6502-retro/6502-retro-v4/hardware/6502-retro-v4.kicad_sch

## KiCad design hardware/6502-retro-v4.kicad_sch (2026-03-13)

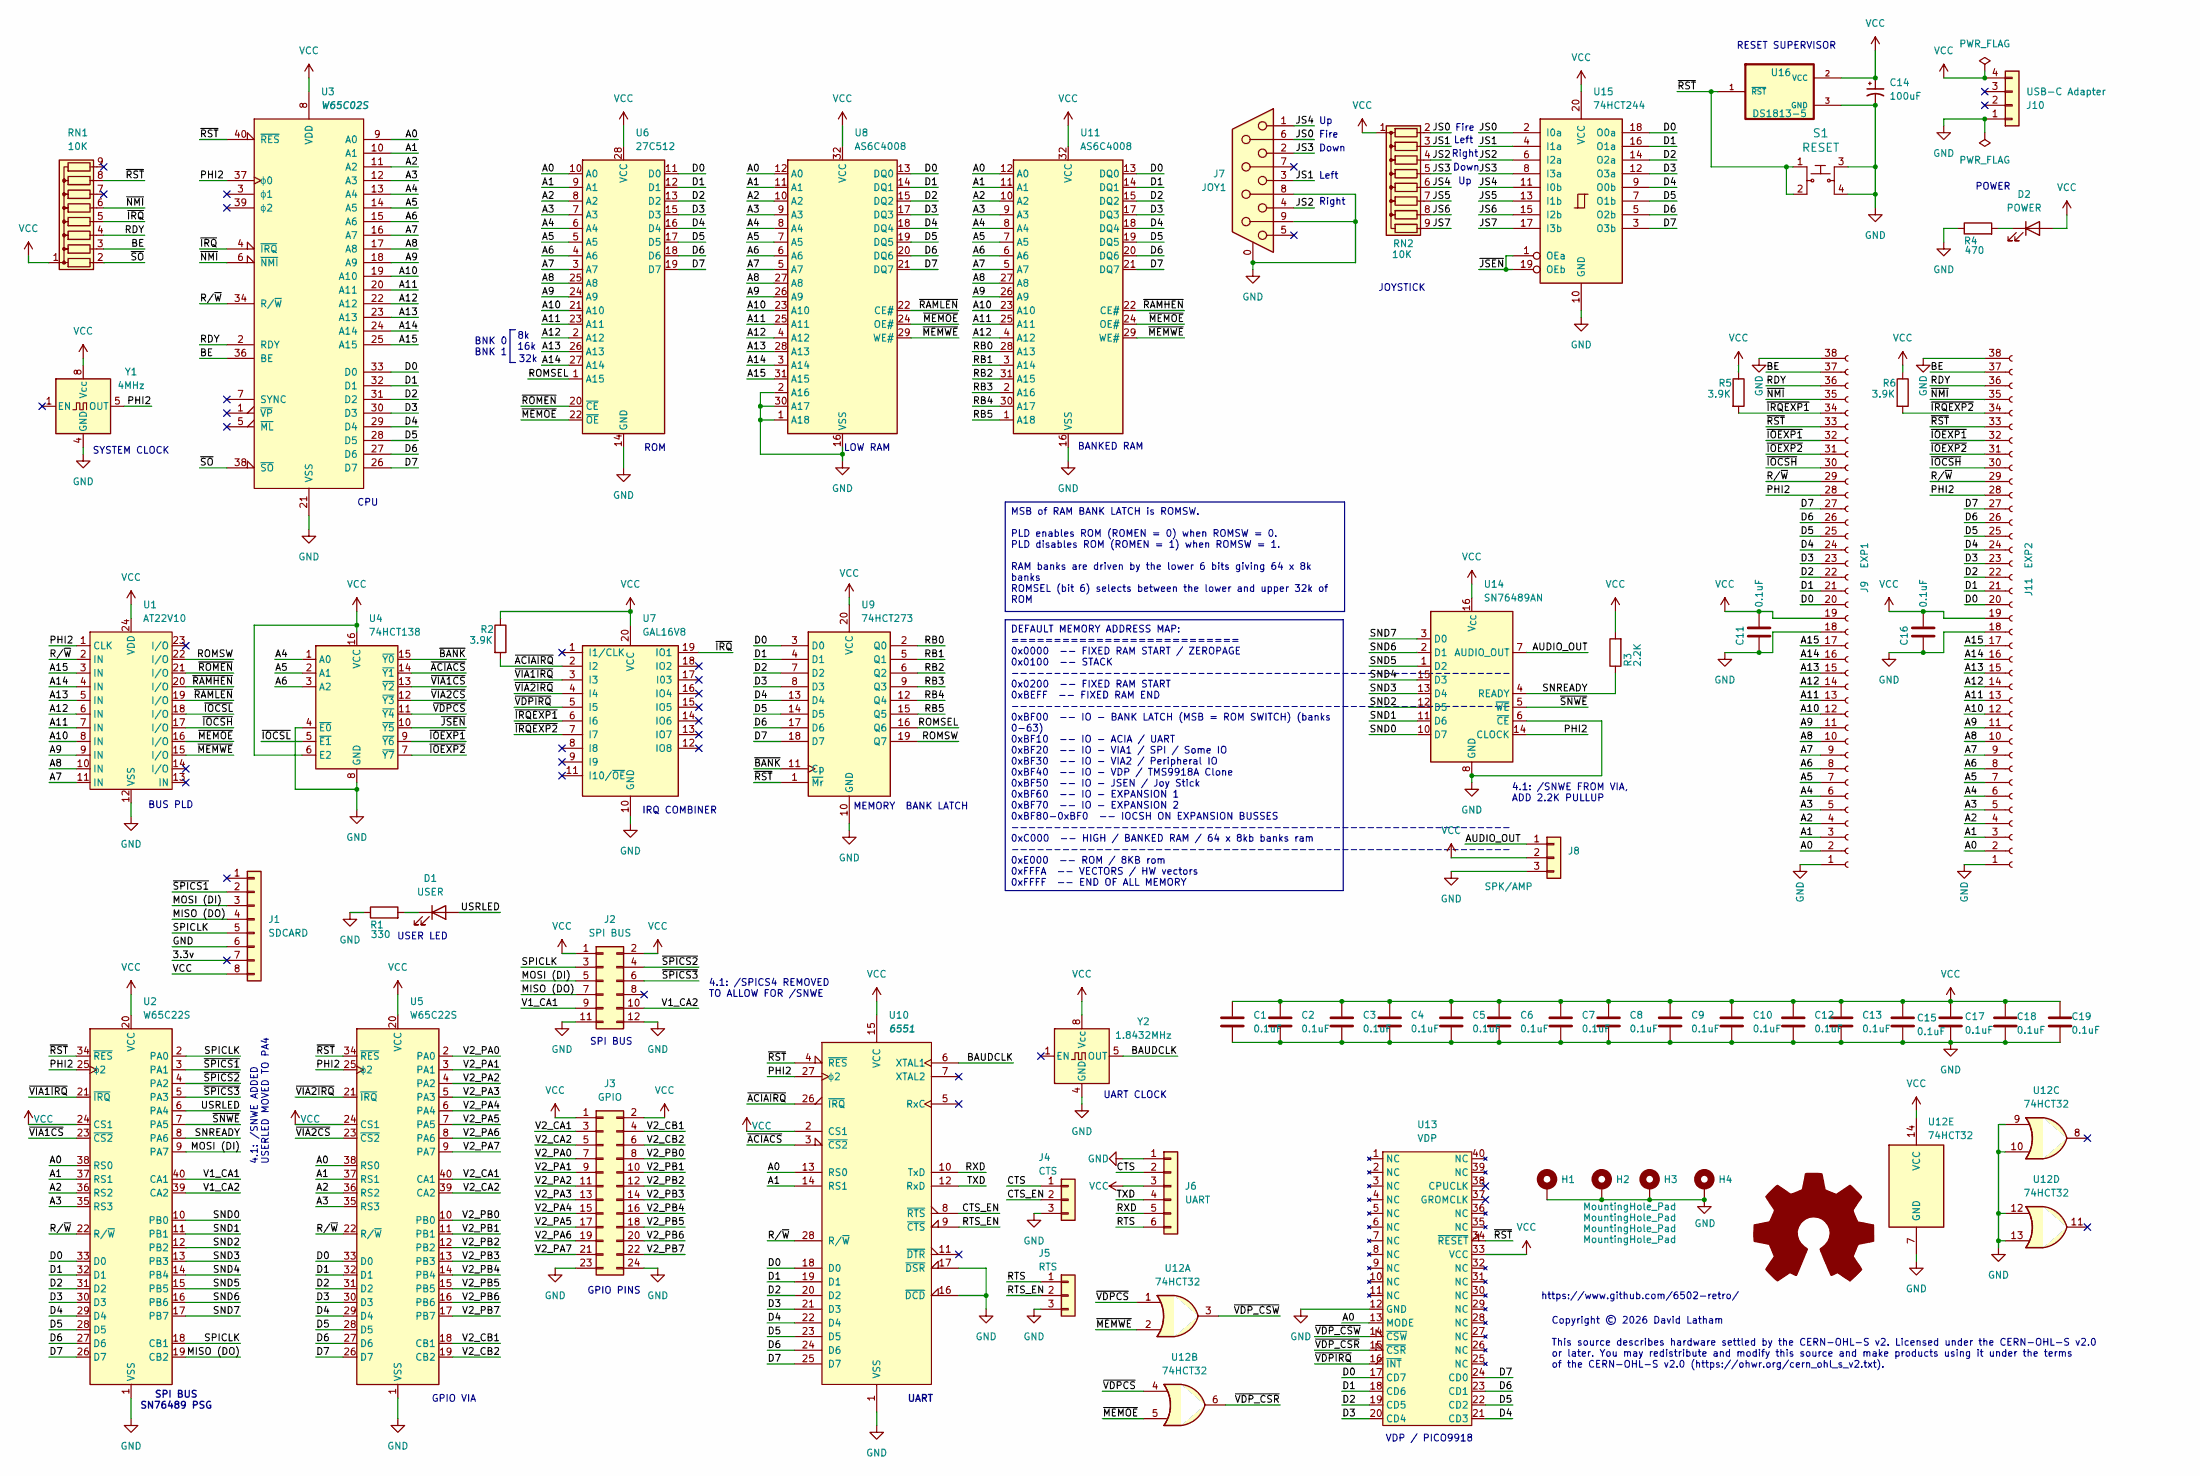
[picture p3: schematic 6502-retro-v4.kicad_sch]

Parts:
C1, C2, C3, C5: 0.1uF; C_Disc_D3.8mm_W2.6mm_P2.50mm
C4, C6, C7, C8, C9, C10, C11, C12, C13, C15, C16, C17, C18, C19: 0.1uF; C_Disc_D3.0mm_W2.0mm_P2.50mm
C14: 100uF; CP_Radial_D5.0mm_P2.50mm
D1: USER; LED_D5.0mm
D2: POWER; LED_D5.0mm
H1, H2, H3, H4: MountingHole_Pad; MountingHole_3.2mm_M3_Pad
J1: SDCARD; PinSocket_1x08_P2.54mm_Vertical
J2: SPI BUS; PinSocket_2x06_P2.54mm_Vertical
J3: GPIO; PinSocket_2x12_P2.54mm_Vertical
J4: CTS; PinHeader_1x03_P2.54mm_Vertical
J5: RTS; PinHeader_1x03_P2.54mm_Vertical
J6: UART; PinSocket_1x06_P2.54mm_Horizontal
J7: JOY1; DSUB-9_Pins_Horizontal_P2.77x2.84mm_EdgePinOffset7.70mm_Hou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
J8: SPK/AMP; PinSocket_1x03_P2.54mm_Vertical
J9: EXP1; PinSocket_1x38_P2.54mm_Vertical
J10: USB-C Adapter; PinSocket_1x04_P2.54mm_Vertical
J11: EXP2; PinSocket_1x38_P2.54mm_Vertical
R1: 330; R_Axial_DIN0204_L3.6mm_D1.6mm_P5.08mm_Horizontal
R2, R5, R6: 3.9K; R_Axial_DIN0204_L3.6mm_D1.6mm_P5.08mm_Horizontal
R3: 2.2K; R_Axial_DIN0204_L3.6mm_D1.6mm_P5.08mm_Horizontal
R4: 470; R_Axial_DIN0204_L3.6mm_D1.6mm_P5.08mm_Horizontal
RN1, RN2: 10K; R_Array_SIP9
S1: RESET; Switch_Tactile_THT_6x6mm; MPN 1825910-6; Digi-Key_PN 450-1650-ND
U1: AT22V10; DIP-24_W7.62mm_Socket
U2, U5: W65C22S; DIP-40_W15.24mm_Socket
U3: W65C02S; DIP-40_W15.24mm_Socket
U4: 74HCT138; DIP-16_W7.62mm_Socket
U6: 27C512; DIP-28_W15.24mm_Socket
U7: GAL16V8; DIP-20_W7.62mm_Socket
U8, U11: AS6C4008; DIP-32_W15.24mm_Socket
U9: 74HCT273; DIP-20_W7.62mm_Socket
U10: 6551; DIP-28_W15.24mm_Socket
U12: 74HCT32; DIP-14_W7.62mm_Socket
U13: VDP; DIP-40_W15.24mm_Socket
U14: SN76489AN; DIP-16_W7.62mm_Socket
U15: 74HCT244; DIP-20_W7.62mm_Socket
U16: DS1813-5; TO-92L_HandSolder
Y1: 4MHz; Oscillator_DIP-8
Y2: 1.8432MHz; Oscillator_DIP-8

Connections:
3.3v: J1.7
A0: J9.2, J11.2, U2.38 (RS0), U3.9 (A0), U5.38 (RS0), U6.10 (A0), U8.12 (A0), U10.13 (RS0), U11.12 (A0), U13.13 (MODE)
A1: J9.3, J11.3, U2.37 (RS1), U3.10 (A1), U5.37 (RS1), U6.9 (A1), U8.11 (A1), U10.14 (RS1), U11.11 (A1)
A2: J9.4, J11.4, U2.36 (RS2), U3.11 (A2), U5.36 (RS2), U6.8 (A2), U8.10 (A2), U11.10 (A2)
A3: J9.5, J11.5, U2.35 (RS3), U3.12 (A3), U5.35 (RS3), U6.7 (A3), U8.9 (A3), U11.9 (A3)
A4: J9.6, J11.6, U3.13 (A4), U4.1 (A0), U6.6 (A4), U8.8 (A4), U11.8 (A4)
A5: J9.7, J11.7, U3.14 (A5), U4.2 (A1), U6.5 (A5), U8.7 (A5), U11.7 (A5)
A6: J9.8, J11.8, U3.15 (A6), U4.3 (A2), U6.4 (A6), U8.6 (A6), U11.6 (A6)
A7: J9.9, J11.9, U1.11 (IN), U3.16 (A7), U6.3 (A7), U8.5 (A7), U11.5 (A7)
A8: J9.10, J11.10, U1.10 (IN), U3.17 (A8), U6.25 (A8), U8.27 (A8), U11.27 (A8)
A9: J9.11, J11.11, U1.9 (IN), U3.18 (A9), U6.24 (A9), U8.26 (A9), U11.26 (A9)
A10: J9.12, J11.12, U1.8 (IN), U3.19 (A10), U6.21 (A10), U8.23 (A10), U11.23 (A10)
A11: J9.13, J11.13, U1.7 (IN), U3.20 (A11), U6.23 (A11), U8.25 (A11), U11.25 (A11)
A12: J9.14, J11.14, U1.6 (IN), U3.22 (A12), U6.2 (A12), U8.4 (A12), U11.4 (A12)
A13: J9.15, J11.15, U1.5 (IN), U3.23 (A13), U6.26 (A13), U8.28 (A13)
A14: J9.16, J11.16, U1.4 (IN), U3.24 (A14), U6.27 (A14), U8.3 (A14)
A15: J9.17, J11.17, U1.3 (IN), U3.25 (A15), U8.31 (A15)
AUDIO_OUT: J8.1, U14.7 (AUDIO_OUT)
BAUDCLK: U10.6 (XTAL1), Y2.5 (OUT)
BE: J9.37, J11.37, RN1.3 (R2), U3.36 (BE)
CTS: J4.1, J6.2
CTS_EN: J4.2, U10.8 (~RTS)
D0: J9.20, J11.20, U2.33 (D0), U3.33 (D0), U5.33 (D0), U6.11 (D0), U8.13 (DQ0), U9.3 (D0), U10.18 (D0), U11.13 (DQ0), U13.17 (CD7), U15.18 (O0a)
D1: J9.21, J11.21, U2.32 (D1), U3.32 (D1), U5.32 (D1), U6.12 (D1), U8.14 (DQ1), U9.4 (D1), U10.19 (D1), U11.14 (DQ1), U13.18 (CD6), U15.16 (O1a)
D2: J9.22, J11.22, U2.31 (D2), U3.31 (D2), U5.31 (D2), U6.13 (D2), U8.15 (DQ2), U9.7 (D2), U10.20 (D2), U11.15 (DQ2), U13.19 (CD5), U15.14 (O2a)
D3: J9.23, J11.23, U2.30 (D3), U3.30 (D3), U5.30 (D3), U6.15 (D3), U8.17 (DQ3), U9.8 (D3), U10.21 (D3), U11.17 (DQ3), U13.20 (CD4), U15.12 (O3a)
D4: J9.24, J11.24, U2.29 (D4), U3.29 (D4), U5.29 (D4), U6.16 (D4), U8.18 (DQ4), U9.13 (D4), U10.22 (D4), U11.18 (DQ4), U13.21 (CD3), U15.9 (O0b)
D5: J9.25, J11.25, U2.28 (D5), U3.28 (D5), U5.28 (D5), U6.17 (D5), U8.19 (DQ5), U9.14 (D5), U10.23 (D5), U11.19 (DQ5), U13.22 (CD2), U15.7 (O1b)
D6: J9.26, J11.26, U2.27 (D6), U3.27 (D6), U5.27 (D6), U6.18 (D6), U8.20 (DQ6), U9.17 (D6), U10.24 (D6), U11.20 (DQ6), U13.23 (CD1), U15.5 (O2b)
D7: J9.27, J11.27, U2.26 (D7), U3.26 (D7), U5.26 (D7), U6.19 (D7), U8.21 (DQ7), U9.18 (D7), U10.25 (D7), U11.21 (DQ7), U13.24 (CD0), U15.3 (O3b)
GND: C1.2, C2.2, C3.2, C4.2, C5.2, C6.2, C7.2, C8.2, C9.2, C10.2, C11.1, C12.2, C13.2, C14.2, C15.2, C16.1, C17.2, C18.2, C19.2, H1.1, H2.1, H3.1, H4.1, J1.6, J2.11, J2.12, J3.23, J3.24, J4.3, J5.3, J6.1, J7.0 (PAD), J7.8, J7.9, J8.3, J9.1, J9.18, J9.38, J10.1, J11.1, J11.18, J11.38, R1.1, R4.1, S1.3, S1.4, U1.12 (VSS), U2.1 (VSS), U3.21 (VSS), U4.4 (~E0), U4.8 (GND), U5.1 (VSS), U6.14 (GND), U7.10 (GND), U8.1 (A18), U8.2 (A16), U8.16 (VSS), U8.30 (A17), U9.10 (GND), U10.1 (VSS), U10.16 (~DCD), U10.17 (~DSR), U11.16 (VSS), U12.7 (GND), U12.9, U12.10, U12.12, U12.13, U13.12 (GND), U14.6 (~CE), U14.8 (GND), U15.10 (GND), U16.3 (GND), Y1.4 (GND), Y2.4 (GND)
JS0: J7.6, RN2.2 (R1), U15.2 (I0a)
JS1: J7.3, RN2.3 (R2), U15.4 (I1a)
JS2: J7.4, RN2.4 (R3), U15.6 (I2a)
JS3: J7.2, RN2.5 (R4), U15.8 (I3a)
JS4: J7.1, RN2.6 (R5), U15.11 (I0b)
JS5: RN2.7 (R6), U15.13 (I1b)
JS6: RN2.8 (R7), U15.15 (I2b)
JS7: RN2.9 (R8), U15.17 (I3b)
MISO (DO): J1.4, J2.7, U2.19 (CB2)
MOSI (DI): J1.3, J2.5, U2.9 (PA7)
unnamed: D1.1 (K), R1.2
unnamed: D2.1 (K), R4.2
PHI2: J9.28, J11.28, U1.1 (CLK), U2.25 (ϕ2), U3.37 (ϕ0), U5.25 (ϕ2), U10.27 (ϕ2), U14.14 (CLOCK), Y1.5 (OUT)
RB0: U9.2 (Q0), U11.28 (A13)
RB1: U9.5 (Q1), U11.3 (A14)
RB2: U9.6 (Q2), U11.31 (A15)
RB3: U9.9 (Q3), U11.2 (A16)
RB4: U9.12 (Q4), U11.30 (A17)
RB5: U9.15 (Q5), U11.1 (A18)
RDY: J9.36, J11.36, RN1.4 (R3), U3.2 (RDY)
ROMSEL: U6.1 (A15), U9.16 (Q6)
ROMSW: U1.22 (I/O), U9.19 (Q7)
RTS: J5.1, J6.6
RTS_EN: J5.2, U10.9 (~CTS)
RXD: J6.5, U10.10 (TxD)
R/~W: J9.29, J11.29, U1.2 (IN), U2.22 (R/~W), U3.34 (R/~W), U5.22 (R/~W), U10.28 (R/~W)
SND0: U2.10 (PB0), U14.10 (D7)
SND1: U2.11 (PB1), U14.11 (D6)
SND2: U2.12 (PB2), U14.12 (D5)
SND3: U2.13 (PB3), U14.13 (D4)
SND4: U2.14 (PB4), U14.15 (D3)
SND5: U2.15 (PB5), U14.1 (D2)
SND6: U2.16 (PB6), U14.2 (D1)
SND7: U2.17 (PB7), U14.3 (D0)
SNREADY: R3.1, U2.8 (PA6), U14.4 (READY)
SPICLK: J1.5, J2.3, U2.2 (PA0), U2.18 (CB1)
TXD: J6.4, U10.12 (RxD)
USRLED: D1.2 (A), U2.6 (PA4)
V1_CA1: J2.9, U2.40 (CA1)
V1_CA2: J2.10, U2.39 (CA2)
V2_CA1: J3.3, U5.40 (CA1)
V2_CA2: J3.5, U5.39 (CA2)
V2_CB1: J3.4, U5.18 (CB1)
V2_CB2: J3.6, U5.19 (CB2)
V2_PA0: J3.7, U5.2 (PA0)
V2_PA1: J3.9, U5.3 (PA1)
V2_PA2: J3.11, U5.4 (PA2)
V2_PA3: J3.13, U5.5 (PA3)
V2_PA4: J3.15, U5.6 (PA4)
V2_PA5: J3.17, U5.7 (PA5)
V2_PA6: J3.19, U5.8 (PA6)
V2_PA7: J3.21, U5.9 (PA7)
V2_PB0: J3.8, U5.10 (PB0)
V2_PB1: J3.10, U5.11 (PB1)
V2_PB2: J3.12, U5.12 (PB2)
V2_PB3: J3.14, U5.13 (PB3)
V2_PB4: J3.16, U5.14 (PB4)
V2_PB5: J3.18, U5.15 (PB5)
V2_PB6: J3.20, U5.16 (PB6)
V2_PB7: J3.22, U5.17 (PB7)
VCC: C1.1, C2.1, C3.1, C4.1, C5.1, C6.1, C7.1, C8.1, C9.1, C10.1, C11.2, C12.1, C13.1, C14.1, C15.1, C16.2, C17.1, C18.1, C19.1, D2.2 (A), J1.8, J2.1, J2.2, J3.1, J3.2, J6.3, J8.2, J9.19, J10.4, J11.19, R2.1, R3.2, R5.1, R6.1, RN1.1 (common), RN2.1 (common), U1.24 (VDD), U2.20 (VCC), U2.24 (CS1), U3.8 (VDD), U4.6 (E2), U4.16 (VCC), U5.20 (VCC), U5.24 (CS1), U6.28 (VCC), U7.20 (VCC), U8.32 (VCC), U9.20 (VCC), U10.2 (CS1), U10.15 (VCC), U11.32 (VCC), U12.14 (VCC), U13.33 (VCC), U14.16 (V_{CC}), U15.20 (VCC), U16.2 (VCC), Y1.8 (Vcc), Y2.8 (Vcc)
~ACIACS: U4.14 (~Y1), U10.3 (~CS2)
~ACIAIRQ: R2.2, U7.2 (I2), U10.26 (~IRQ)
~BANK: U4.15 (~Y0), U9.11 (Cp)
~IOCSH: J9.30, J11.30, U1.17 (I/O)
~IOCSL: U1.18 (I/O), U4.5 (~E1)
~IOEXP1: J9.32, J11.32, U4.9 (~Y6)
~IOEXP2: J9.31, J11.31, U4.7 (~Y7)
~IRQEXP1: J9.34, R5.2, U7.6 (I6)
~IRQEXP2: J11.34, R6.2, U7.7 (I7)
~IRQ: RN1.5 (R4), U3.4 (~IRQ), U7.19 (IO1)
~JSEN: U4.10 (~Y5), U15.1 (OEa), U15.19 (OEb)
~MEMOE: U1.16 (I/O), U6.22 (~OE), U8.24 (OE#), U11.24 (OE#), U12.5
~MEMWE: U1.15 (I/O), U8.29 (WE#), U11.29 (WE#), U12.2
~NMI: J9.35, J11.35, RN1.6 (R5), U3.6 (~NMI)
~RAMHEN: U1.20 (I/O), U11.22 (CE#)
~RAMLEN: U1.19 (I/O), U8.22 (CE#)
~ROMEN: U1.21 (I/O), U6.20 (~CE)
~RST: J9.33, J11.33, RN1.8 (R7), S1.1, S1.2, U2.34 (~RES), U3.40 (~RES), U5.34 (~RES), U9.1 (~Mr), U10.4 (~RES), U13.34 (~RESET), U16.1 (~RST)
~SNWE: U2.7 (PA5), U14.5 (~WE)
~SO: RN1.2 (R1), U3.38 (~SO)
~SPICS1: J1.2, U2.3 (PA1)
~SPICS2: J2.4, U2.4 (PA2)
~SPICS3: J2.6, U2.5 (PA3)
~VDPCS: U4.11 (~Y4), U12.1, U12.4
~VDPIRQ: U7.5 (I5), U13.16 (~INT)
~VDP_CSR: U12.6, U13.15 (~CSR)
~VDP_CSW: U12.3, U13.14 (~CSW)
~VIA1CS: U2.23 (~CS2), U4.13 (~Y2)
~VIA1IRQ: U2.21 (~IRQ), U7.3 (I3)
~VIA2CS: U4.12 (~Y3), U5.23 (~CS2)
~VIA2IRQ: U5.21 (~IRQ), U7.4 (I4)

Notes on the sheet:
LOW RAM
GPIO PINS
USER LED
4.1: /SNWE ADDED USERLED MOVED TO PA4
RESET SUPERVISOR
Fire
Copyright © 2026 David Latham This source describes hardware settled by the CERN-OHL-S v2. Licensed under the CERN-OHL-S v2.0 or later. You may redistribute and modify this source and make products using it under the terms of the CERN-OHL-S v2.0 (https://ohwr.org/cern_ohl_s_v2.txt).
Left
SPI BUS SN76489 PSG
CPU
Down
4.1: /SPICS4 REMOVED TO ALLOW FOR /SNWE
https://www.github.com/6502-retro/
VDP / PICO9918
16k
ROM
Right
4.1: /SNWE FROM VIA, ADD 2.2K PULLUP
JOYSTICK
BUS PLD
SYSTEM CLOCK
POWER
BANKED RAM
BNK 0 BNK 1
SPI BUS
UART CLOCK
MEMORY BANK LATCH
32k
UART
IRQ COMBINER
GPIO VIA
MSB of RAM BANK LATCH is ROMSW. PLD enables ROM (ROMEN = 0) when ROMSW = 0. PLD disables ROM (ROMEN = 1) when ROMSW = 1. RAM banks are driven by the lower 6 bits giving 64 x 8k banks ROMSEL (bit 6) selects between the lower and upper 32k of ROM
DEFAULT MEMORY ADDRESS MAP: =========================== 0x0000 -- FIXED RAM START / ZEROPAGE 0x0100 -- STACK ----------------------------------------------------------- 0x0200 -- FIXED RAM START 0xBEFF -- FIXED RAM END ----------------------------------------------------------- 0xBF00 -- IO - BANK 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
